connormichalec/395-Melodica/STM32CubeIDEProjects/V2/melodica_aeffects_synthesis/Core/Src/voice.c

/*
 * voice.c
 *
 * An encapsulation of a "sound" can have multiple oscillators, ADSR, etc...
 *
 *  Created on: Apr 16, 2025
 *      Author: Connor Michalec
 */

#include "voice.h"
#include <stddef.h>
#include "midi.h"
#include "signal.h"

// Number of voices
Voice voices[NUM_VOICES_MAX];
int num_voices_enabled;

int get_num_voices() {
	return NUM_VOICES_MAX;
}

int num_enabled_voices() {
	return num_voices_enabled;
}

int getFirstDisabledVoiceIdx() {
	for(int x = 0; x<NUM_VOICES_MAX; x++) {
		if(voices[x].enabled==0) {
			return x;
		}
	}
	return -1;
}

void init_voices() {
	init_oscillators();
	init_adsrs();

	for(int i = 0; i<NUM_VOICES_MAX; i++) {
		for(int x = 0; x<VOICE_NUM_OSC_MAX; x++) {
			voices[i].osc[x] = NULL;
		}
		voices[i].enabled = 0;
		voices[i].adsr = NULL;
		voices[i].voice_num_oscillators = 0;
		voices[i].NOTE = -1;
		voices[i].channel = -1;
		voices[i].base_freq = 0;
		voices[i].detune = 0.0f;
		voices[i].filters = NULL;		// Head to linked list is null
	}
}

void tick_voices() {
	// Tick all voices
	for(int i = 0; i < NUM_VOICES_MAX; i++) {
		if(voices[i].enabled) {
			tick_voice(&voices[i]);
		}
	}
}

void tick_voice(Voice * voice) {
	if(voice == NULL || !voice->enabled)
		return;

	//Tick ADSRs:
	ADSR_tick(voice->adsr);

	//If ADSR is set to DONE state, disable this voice as it is done playing until re-enabled.
	if(voice->adsr->cur_state == DONE)
		disable_voice(voice);

}

float get_voice_ADSR_val(Voice * voice) {
	if(voice->adsr==NULL)
		return 1.0;
	return(voice->adsr->cur_val);
}


int get_voice_channel(Voice * voice) {
	return(voice->channel);
}

void set_voice_channel(Voice * voice, int newChannel) {
	voice->channel = newChannel;
}

void add_voice_ADSR(Voice * voice, float attack_factor, float attack_level, float decay_factor, float sustain_level, float release_factor) {
	// Create adsr for this voice:
	voice->adsr = create_ADSR(attack_factor,attack_level,decay_factor,sustain_level,release_factor);

	// Go to attack phase of adsr
	ADSR_next(voice->adsr);
}

ADSR* get_voice_ADSR(Voice * voice) {
	return(voice->adsr);
}

void add_voice_filter(Voice * voice, FilterType type, float cutoff, float resonance) {

	// New filter
	Filter * newFilter = create_filter(cutoff, resonance, type);

	// Find linked list end:

	Filter * f = voice->filters;
	if(f==NULL) {
		// Root node is null, create new root
		voice->filters = newFilter;
		return;
	}
	else {
		while(f->next!=NULL) {
			f = f->next;
		}
	}

	// Append filter to end of linked list:
	f->next = newFilter;
}

Filter * get_voice_filters(Voice * v) {
	return v->filters;
}

int get_num_filters(Voice * v) {
	Filter * f =v->filters;

	int idx = 0;

	while(f!=NULL) {
		idx++;
		f = f->next;
	}

	return idx;
}

void construct_voice(oscillatorTypes type, Voice * v, float frequency, float detune) {
	v->enabled = 1;
	v->channel = 0;

	v->base_freq = frequency;


	for(int i =0; i<VOICE_NUM_OSC_MAX && i < v->voice_num_oscillators; i++) {
		v->osc[i] = get_oscillator(enable_oscillator(type, frequency));
	}

	// Set detune:
	set_voice_detune(v, detune);
}

int enable_voice(oscillatorTypes type, int numOscillators, int note, float detune) {
	int idx = getFirstDisabledVoiceIdx();

	// No voices avail
	if(idx == -1) return -1;

	Voice * v = get_voice_from_idx(idx);


	// Make sure there are enough oscillators available for this Voice to be enabled:
	if(numOscillators > get_num_oscillators()-num_enabled_oscillators()) {
		return -1;
	}

	v->voice_num_oscillators = numOscillators;


	// Check if this note is already active:
	if(get_voice_from_note(note)!=NULL) {
		// Already a voice with this note, disable that voice:
		disable_voice(get_voice_from_note(note));
	}


	// Create new voice with this note:
	v->NOTE = note;

	construct_voice(type, v, ToFrequency(note), detune);

	num_voices_enabled++;

	return idx;
}

void disable_voice(Voice * voice) {

	// Check if voice is actually enabled:
	if(voice==NULL || !voice->enabled)
		return;

	// Disable all oscillators associated w/
	for(int i =0; i<voice->voice_num_oscillators; i++) {
		disable_oscillator(voice->osc[i]);
		voice->osc[i] = NULL;
	}


	// Delete ADSR
	delete_ADSR(voice->adsr);
	// Delete filters:
	Filter * f = voice->filters;
	while(f!=NULL) {
		Filter * fprev = f;
		f = f->next;
		delete_filter(fprev);
	}

	voice->adsr = NULL;
	voice->enabled = 0;
	voice->voice_num_oscillators = 0;
	voice->NOTE = -1;
	voice->channel = -1;
	voice->base_freq = 0;
	voice->detune = 0.0f;
	voice->filters = NULL;

	num_voices_enabled--;

}

void set_voice_oscillators(Voice* v, int numOscillators, oscillatorTypes type, float frequency) {

	// Go through each existing oscillator and make sure it matches the new type:
	for(int i = 0; i< v->voice_num_oscillators; i++) {
		if(get_oscillator_type(v->osc[i]) != type) {
			set_oscillator_type(v->osc[i], type);
		}
	}


	// Check to see if number have oscillators has changed.
	if(v->voice_num_oscillators != numOscillators) {
		int newAmount = v->voice_num_oscillators;

		if(numOscillators < v->voice_num_oscillators) {
			// Need to disable some oscillators from the voice, disable last N oscillators

			for(int i = v->voice_num_oscillators-1; i >= numOscillators && i>= 0; i--) {
				disable_oscillator(v->osc[i]);
				v->osc[i] = NULL;

				newAmount--;
			}

		}
		else {

			// If there are enough available oscillators, more up until numOscillators or we run out of oscillators/ run into limit.
			for(int i = v->voice_num_oscillators-1; i < numOscillators && i < get_num_oscillators()-num_enabled_oscillators() && i< VOICE_NUM_OSC_MAX; i++) {
				v->osc[i] = get_oscillator(enable_oscillator(type, frequency));
				newAmount++;
			}

		}

		// Apply detune to all oscillators again:
		set_voice_detune(v, v->detune);

		v->voice_num_oscillators = newAmount;
	}
}

float get_voice_detune(Voice * voice) {
	return(voice->detune);
}

float detune_scale = 7.0f;
void set_voice_detune(Voice * voice, float detune) {
	if(detune<=0.0f)
		detune = 0.0f;
	if(detune>=1.0f)
		detune = 1.0f;
	voice->detune = detune;
	float frequency = voice->base_freq;
	// Update oscillator frequencies accordingly:
	for(int i =0; i<VOICE_NUM_OSC_MAX; i++) {
		// Alternate whether detune adds or subtracts to frequency based on if i is odd or even (creates even spread):
		// detune/VOICE_NUM_OSC so that there is the same amount of detune regardless of the amount of oscillators.
		voice->osc[i]->frequency = i%2==0 ? (frequency + (float)i * (detune*detune_scale)/VOICE_NUM_OSC_MAX) : (frequency - (float)i * (detune*detune_scale)/VOICE_NUM_OSC_MAX);

	}
}


Voice * get_voice_from_idx(int voice_idx) {
	if(voice_idx==-1)
		return NULL;

	return &voices[voice_idx];
}

Voice * get_voice_from_note(int note) {
	if(note==-1)
		return NULL;

	for(int i = 0; i<NUM_VOICES_MAX; i++) {
		if(voices[i].NOTE==note) {
			return(&voices[i]);
		}
	}
	return NULL;
}
