connormichalec/395-Melodica/STM32CubeIDEProjects/V2/melodica_switchbox_boilerplate/Core/Inc/config.h

/*
 * config.h
 *
 *  Created on: Oct 13, 2025
 *      Author: kobes
 */

#define DEVICE_ID 2
#define UPDATE_MSG_PERIOD_MS 1000
#define IO_POLL_MSG_PERIOD_MS 80		// this cant be too small, otherwise parameters will fail to send properly
