connormichalec/395-Melodica/STM32CubeIDEProjects/V2/melodica_looper/Core/Inc/modules.h

/*
 * modules.h
 *
 *  Created on: Sep 18, 2025
 *      Author: kobes
 */

#ifndef INC_MODULES_H_
#define INC_MODULES_H_

#include "stm32g4xx_hal.h"

extern UART_HandleTypeDef huart1;
extern uint32_t last_rx_timestamp;

// Module ID definitions
#define MODULE_CONNECTIVITY_MSG 0
#define MODULE_TRANSPOSE_ID 1
#define MODULE_STOPS_ID 2
#define MODULE_LOOPER_ID 3
#define MODULE_ARP_ID 4
#define MODULE_SYNTH_ID 255

// Configurable parameters
#define MODULE_UART huart1

// Constant definitions
#define MODULE_RX_TIMEOUT_MS 100

#define CONNECTIVITY_MSG_LEN 2
#define MAX_TRANSPOSE_RANGE 12

// Button definitions
#define BUTTON_TRANSPOSE_DOWN 0
#define BUTTON_TRANSPOSE_UP 1


// Internal module struct
typedef struct ModuleStream ModuleStream;
struct ModuleStream {
	uint8_t data[512];
	uint16_t data_idx;
	void (*update_noteoff)(ModuleStream*, uint8_t, uint8_t, uint8_t);	// Channel, key, velocity
	void (*update_noteon)(ModuleStream*, uint8_t, uint8_t, uint8_t);	// Channel, key, velocity
	void (*update_channelpressure)(ModuleStream*, uint8_t, uint8_t);	// Channel, pressure
	void (*update_tick)(uint32_t);	// Timestamp
};

extern ModuleStream* streams[16];
extern ModuleStream out_stream;
extern ModuleStream transpose_stream;

// State structs
typedef struct TransposeState {
	int8_t shift;
} TransposeState;

extern TransposeState transpose_state;

void stream_noteon(ModuleStream* module, uint8_t channel, uint8_t key, uint8_t velocity);
void stream_noteoff(ModuleStream* module, uint8_t channel, uint8_t key, uint8_t velocity);

typedef struct StopsState {
	uint8_t stops[4];
} StopsState;

extern StopsState stops_state;

typedef struct LooperState {
	uint8_t connected;
} LooperState;

typedef struct PressureToggleState{
	uint8_t pressure_enabled;
} PressureToggleState;

extern PressureToggleState pressure_toggle_state;

void Module_Init();
void send_msg(uint8_t device, uint8_t *data, uint8_t len);

void MIDI_RunModules();
void Module_ProcessByte();
void append_byte(ModuleStream* module, uint8_t byte);

void handle_connectivity_msg(uint8_t device_id, uint16_t idx);
void handle_looper_msg(uint8_t* data, uint8_t len);
void handle_transpose_msg(uint8_t* data, uint8_t len);
void handle_stops_msg(uint8_t* data, uint8_t len);

void noupdate_channelpressure(ModuleStream* stream, uint8_t channel, uint8_t pressure);
void out_stream_update_noteon(ModuleStream* stream, uint8_t channel, uint8_t key, uint8_t velocity);
void out_stream_update_noteoff(ModuleStream* stream, uint8_t channel, uint8_t key, uint8_t velocity);
void out_stream_update_channelpressure(ModuleStream* stream, uint8_t channel, uint8_t pressure);
void transpose_update_noteon(ModuleStream* stream, uint8_t channel, uint8_t key, uint8_t velocity);
void transpose_update_noteoff(ModuleStream* stream, uint8_t channel, uint8_t key, uint8_t velocity);
void stops_update_noteon(ModuleStream* stream, uint8_t channel, uint8_t key, uint8_t velocity);
void stops_update_noteoff(ModuleStream* stream, uint8_t channel, uint8_t key, uint8_t velocity);


#endif /* INC_MODULES_H_ */
