connormichalec/395-Melodica/STM32CubeIDEProjects/V2/melodica_aeffects_synthesis/Core/Inc/oscillator.h

/*
 * oscillator.h
 *
 *  Created on: Apr 4, 2025
 *      Author: conno
 */

#ifndef SRC_OSCILLATOR_H_
#define SRC_OSCILLATOR_H_

#define NUM_OSCILLATORS 48

typedef enum {
	NOTYPE,
	SIN,
	SAW,
	SQUARE
} oscillatorTypes;

typedef struct {
	oscillatorTypes type;
	float (*oscillatorFunction)(float phase);			// Function to get an oscillation based on phase (based on the type)
	float phase;
	float frequency;
	int osc_idx;										// Oscillator index (for easy indexing of all oscillators)
	int enabled;										// Is this oscillator enabled?
} Oscillator;

/**
 * Initialize oscillator system
 */
void init_oscillators();

/**
 * Get Total number of oscillators
 */
int get_num_oscillators();

/**
 * Set oscillator type
 */

void set_oscillator_type(Oscillator* osc, oscillatorTypes type);
/**
 * Get oscillator type
 */
oscillatorTypes get_oscillator_type(Oscillator* osc);

/**
 * Get number of oscillators currently enabled
 */
int num_enabled_oscillators();

/**
 * Get oscillator given its idx
 */
Oscillator * get_oscillator(int oscillator_idx);

/**
 * Enable an oscillator
 */
int enable_oscillator(oscillatorTypes oscillator, float frequency);

/**
 * Disable an oscillator
 */
void disable_oscillator(Oscillator * oscillator);

/**
 * Set osc freq
 */
void set_osc_freq(Oscillator * oscillator, float freq);

/**
 * Get osc freq
 */
float get_osc_freq(Oscillator * oscillator);


#endif /* SRC_OSCILLATOR_H_ */
