connormichalec/395-Melodica/Hardware_Controller/Core/Src/mux.h

/*
 * mux.h
 *
 *  Created on: Feb 24, 2025
 *      Author: kobes
 */

#pragma once
#include <stdint.h>
#include "stm32l0xx_hal.h"

void SetSelectBits(uint8_t key);
void ReadKeyboard(uint8_t status[], uint8_t pressure_on);
void tick_buttons();
